hughe349/Senior_Design_IRLTSPICE/firmware/include/main.h

#ifndef __MAIN_H__
#define __MAIN_H__

#ifdef __cplusplus
extern "C"
{
#endif

#include "stm32f0xx_hal.h"
#include "stm32f0xx_hal_uart.h"
#include "stm32f0xx_hal_spi.h"
#include "uart_bytes.h"

#ifdef __cplusplus
}
#endif

#endif /* __MAIN_H__ */
